orpheus016/integrated-iv-points/software/output/ads1256/volt_log_20260526_152836/volt_log_20260526_152836_transient.png

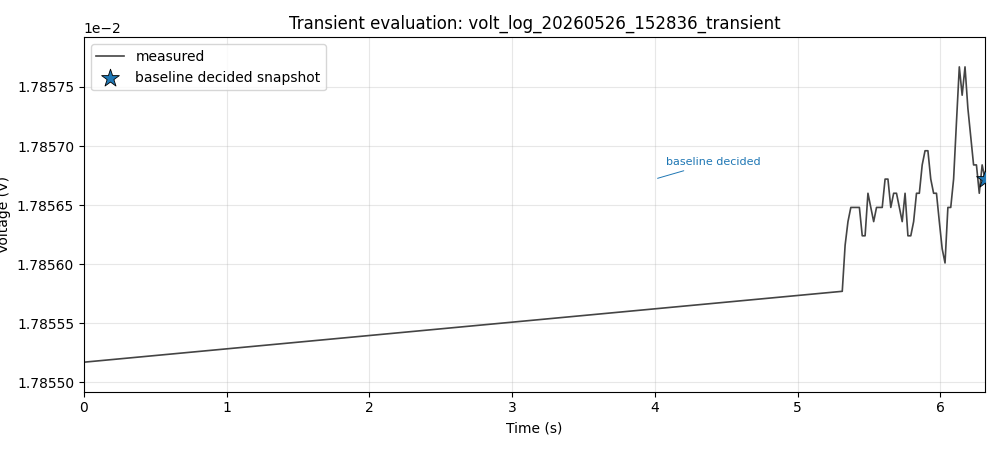
software/output/ads1256/volt_log_20260526_152836/volt_log_20260526_152836_transient.png
