orpheus016/integrated-iv-points/software/output/ads1256/volt_log_20260526_201416/volt_log_20260526_201416_transient.png

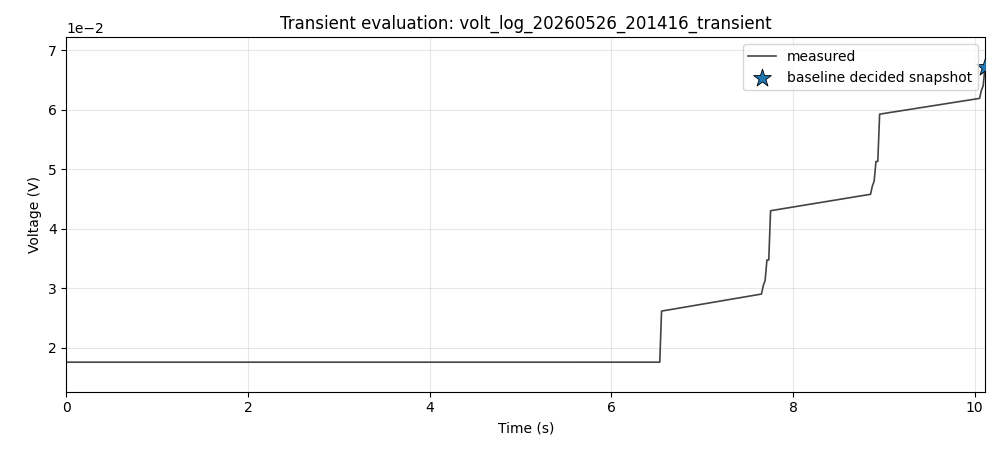
software/output/ads1256/volt_log_20260526_201416/volt_log_20260526_201416_transient.png
