orpheus016/integrated-iv-points/software/output/ads1256/volt_log_20260529_153043/volt_log_20260529_153043_transient.png

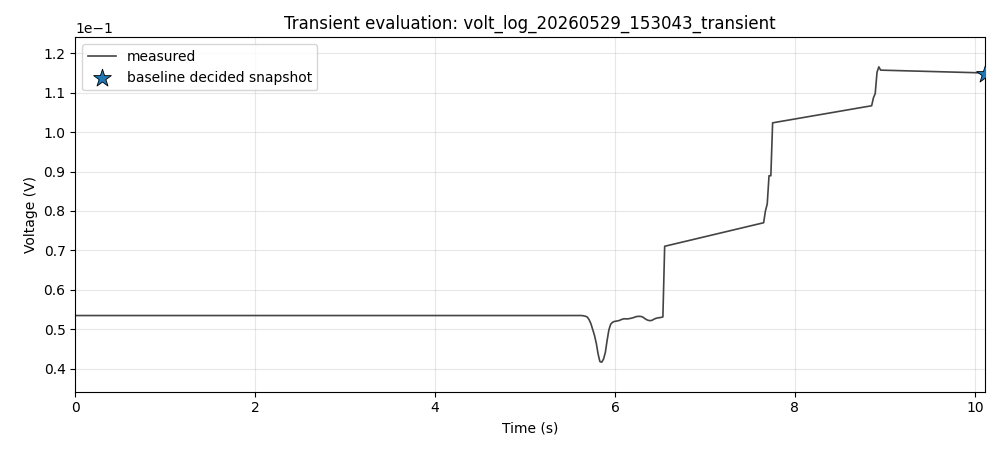
software/output/ads1256/volt_log_20260529_153043/volt_log_20260529_153043_transient.png
