orpheus016/integrated-iv-points/software/output/ads1256/volt_log_20260529_162711/volt_log_20260529_162711_transient.png

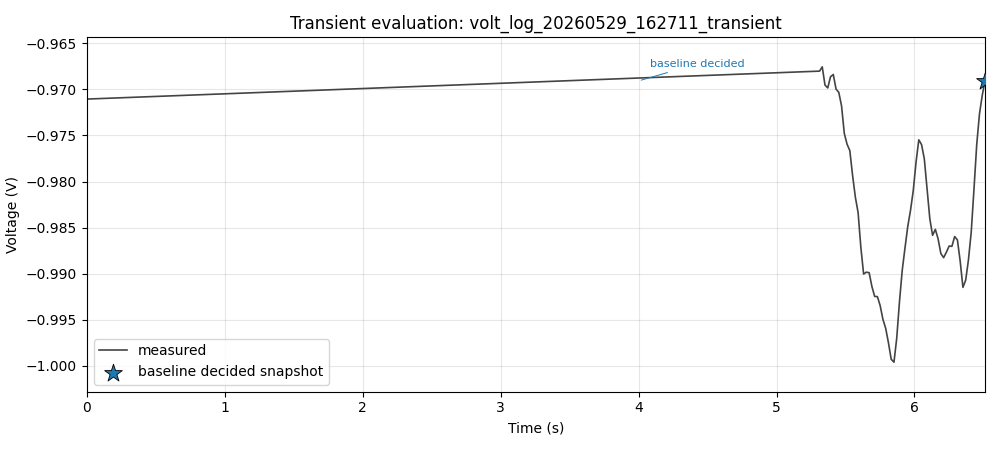
software/output/ads1256/volt_log_20260529_162711/volt_log_20260529_162711_transient.png
