orpheus016/integrated-iv-points/software/output/ads1256/volt_log_20260529_163026/volt_log_20260529_163026_transient.png

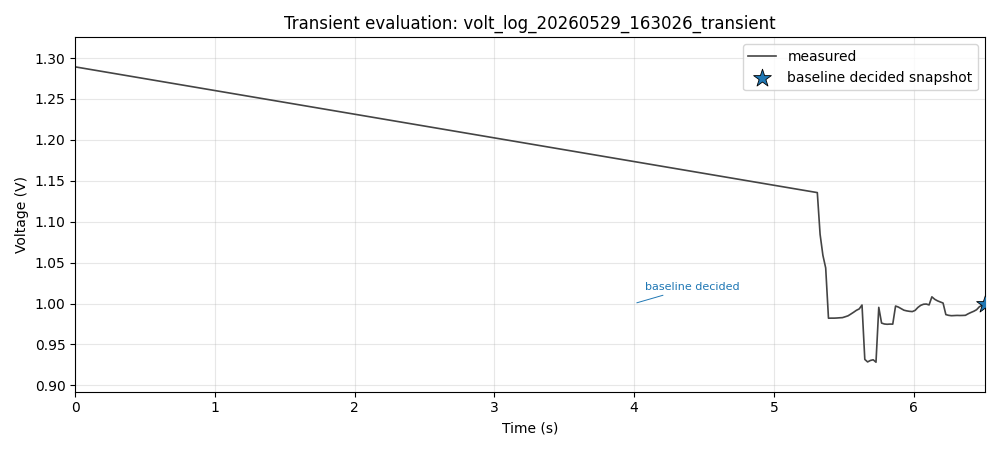
software/output/ads1256/volt_log_20260529_163026/volt_log_20260529_163026_transient.png
