orpheus016/integrated-iv-points/software/output/ads1256/volt_log_20260529_163121/volt_log_20260529_163121_transient.png

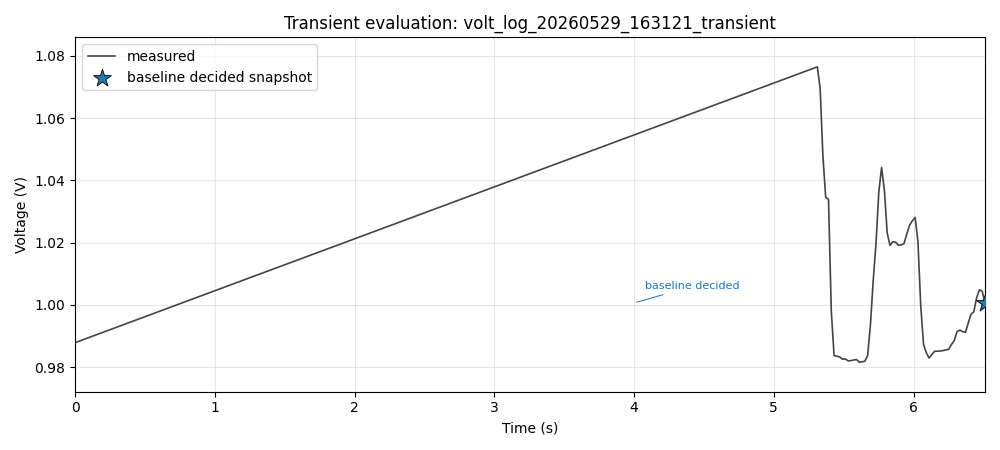
software/output/ads1256/volt_log_20260529_163121/volt_log_20260529_163121_transient.png
