orpheus016/integrated-iv-points/software/output/ads1256/volt_log_20260529_163239/volt_log_20260529_163239_transient.png

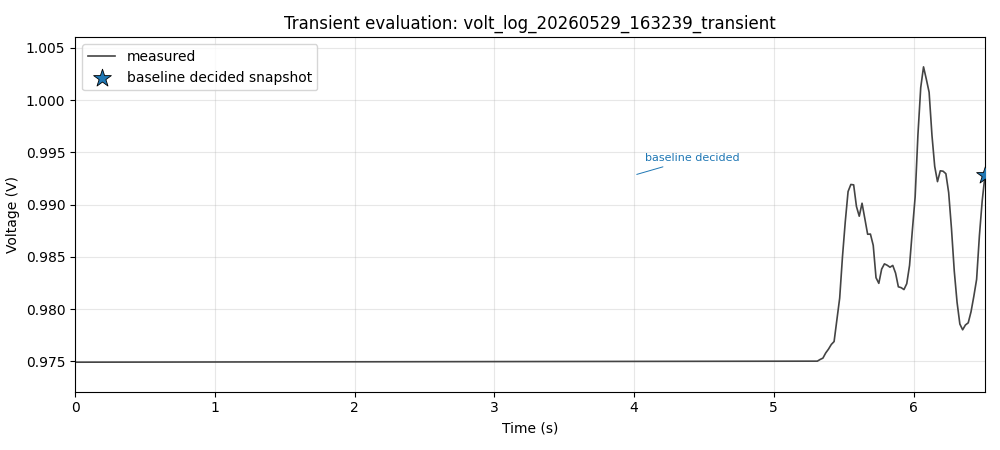
software/output/ads1256/volt_log_20260529_163239/volt_log_20260529_163239_transient.png
