orpheus016/integrated-iv-points/software/output/ads1256/volt_log_20260529_163329/volt_log_20260529_163329_transient.png

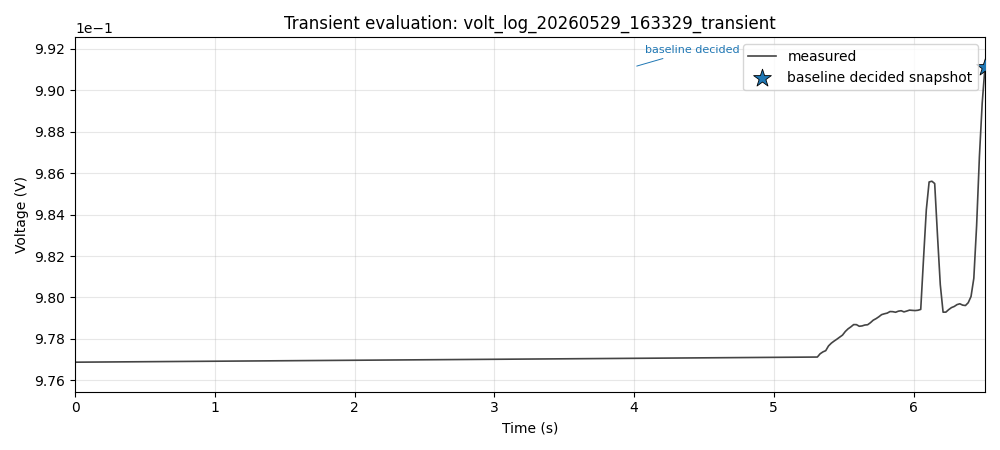
software/output/ads1256/volt_log_20260529_163329/volt_log_20260529_163329_transient.png
