orpheus016/integrated-iv-points/software/plots/output/current_source_consistency/current_source_consistency_plot_integrated.png

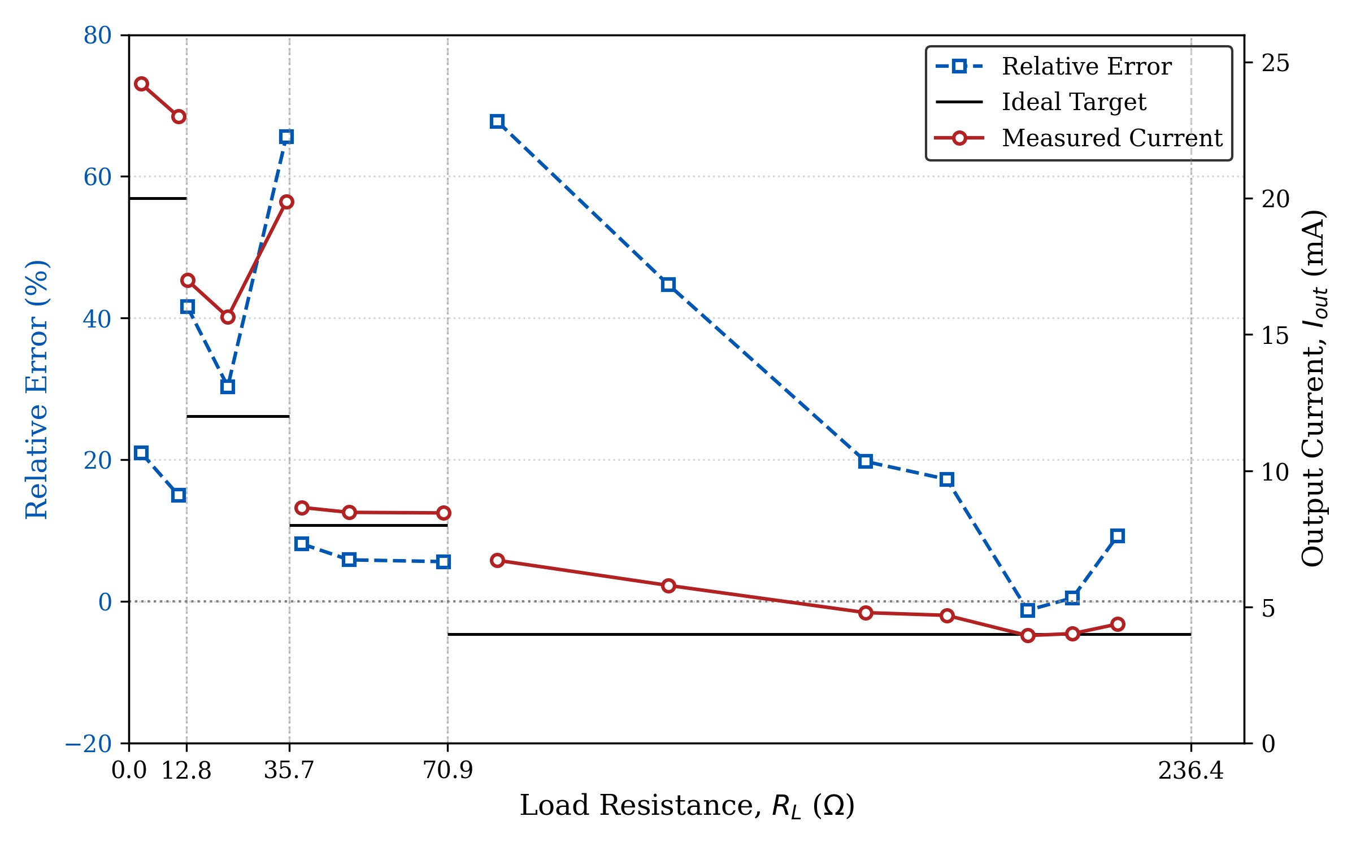
software/plots/output/current_source_consistency/current_source_consistency_plot_integrated.png
