orpheus016/integrated-iv-points/software/plots/output/current_source_consistency/research_grade_stability_plot.png

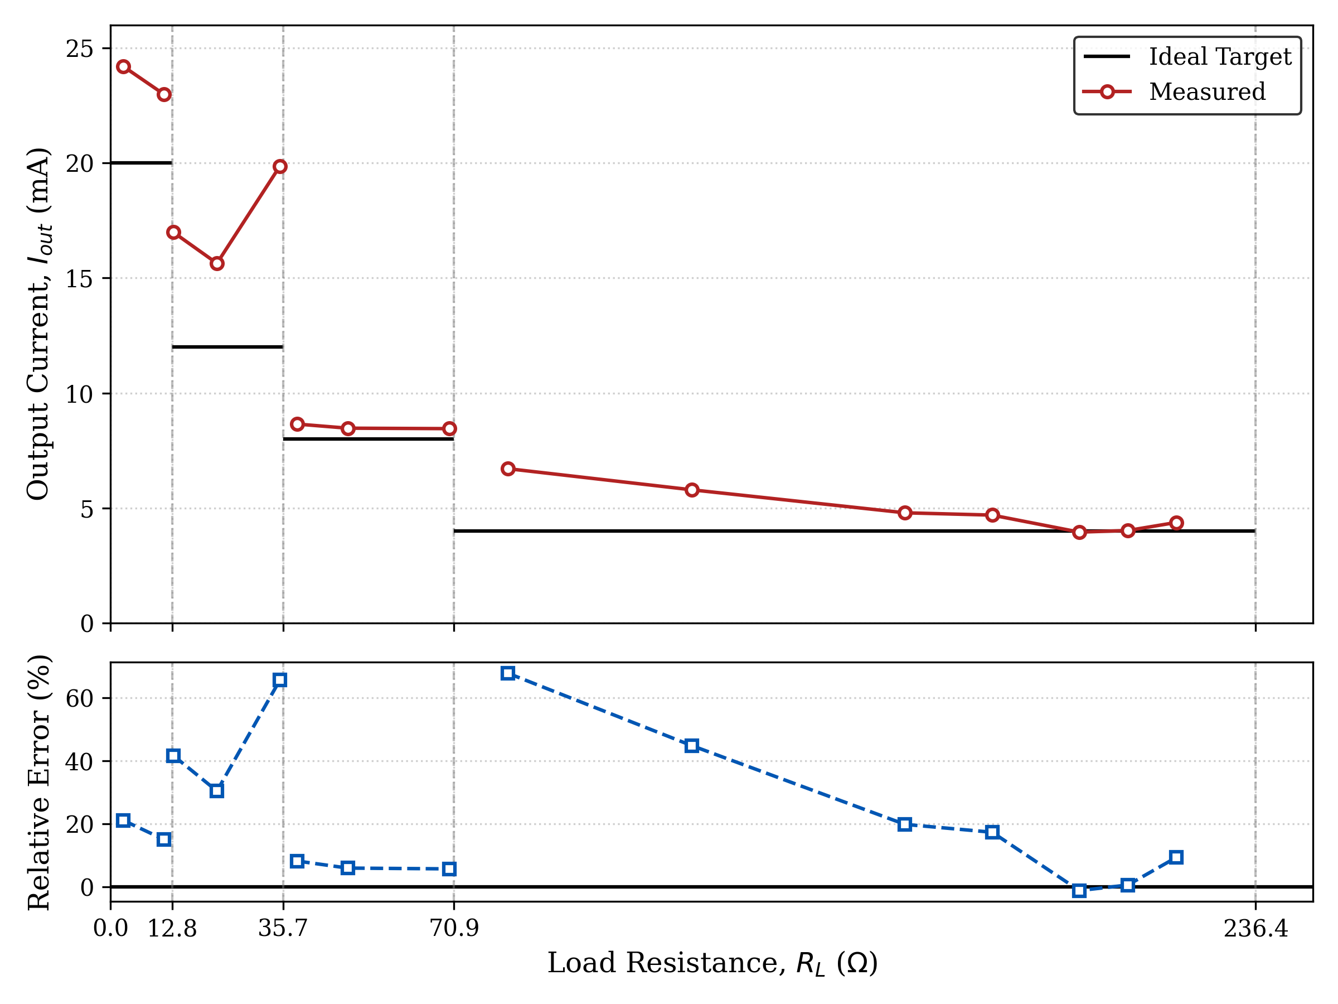
software/plots/output/current_source_consistency/research_grade_stability_plot.png
