orpheus016/integrated-iv-points/software/plots/output/ia_dc/ia_dc_transfer_analysis.png

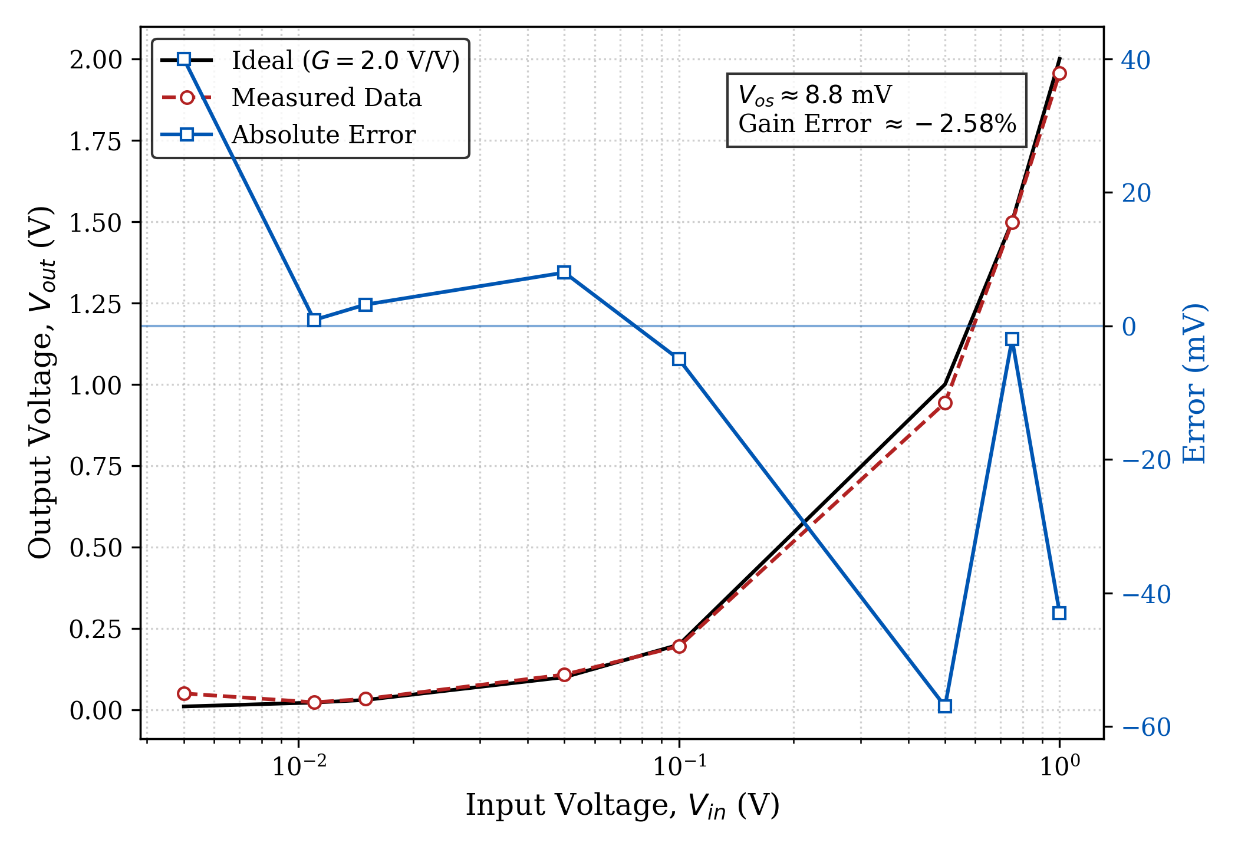
software/plots/output/ia_dc/ia_dc_transfer_analysis.png
