orpheus016/integrated-iv-points/software/plots/output/signal_quality/signal_quality_combined.png

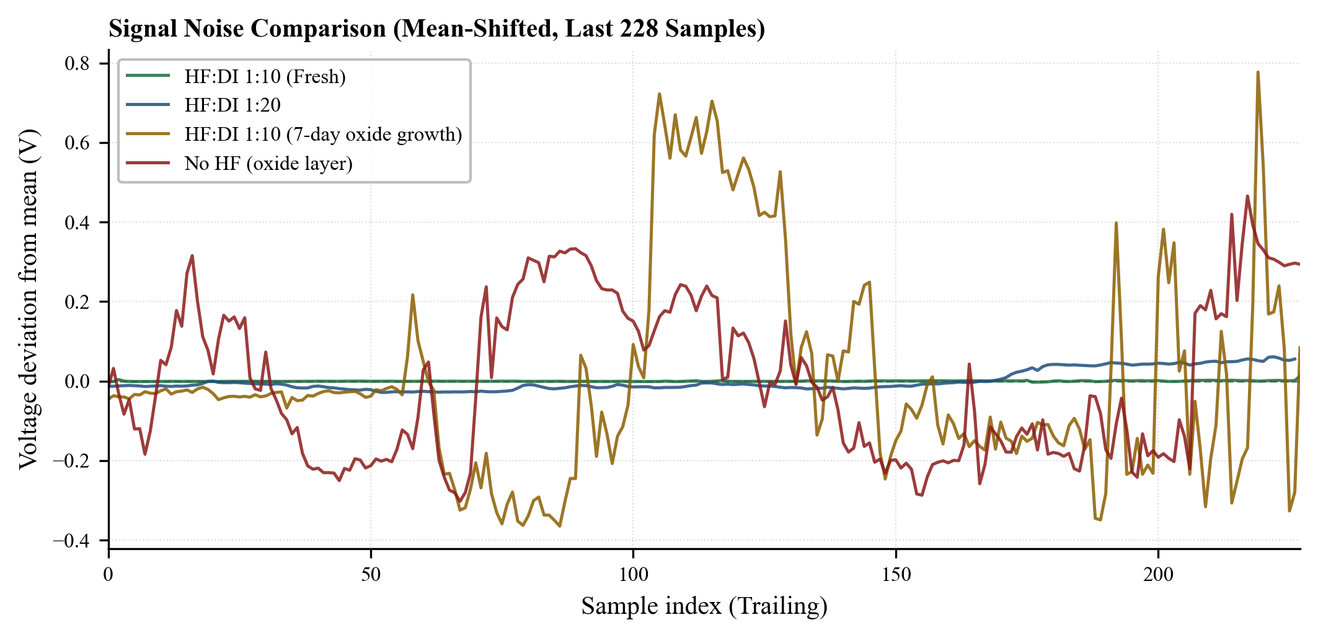
software/plots/output/signal_quality/signal_quality_combined.png
