orpheus016/integrated-iv-points/software/plots/output/temporal_robustness/20260607_012642/boxplot.png

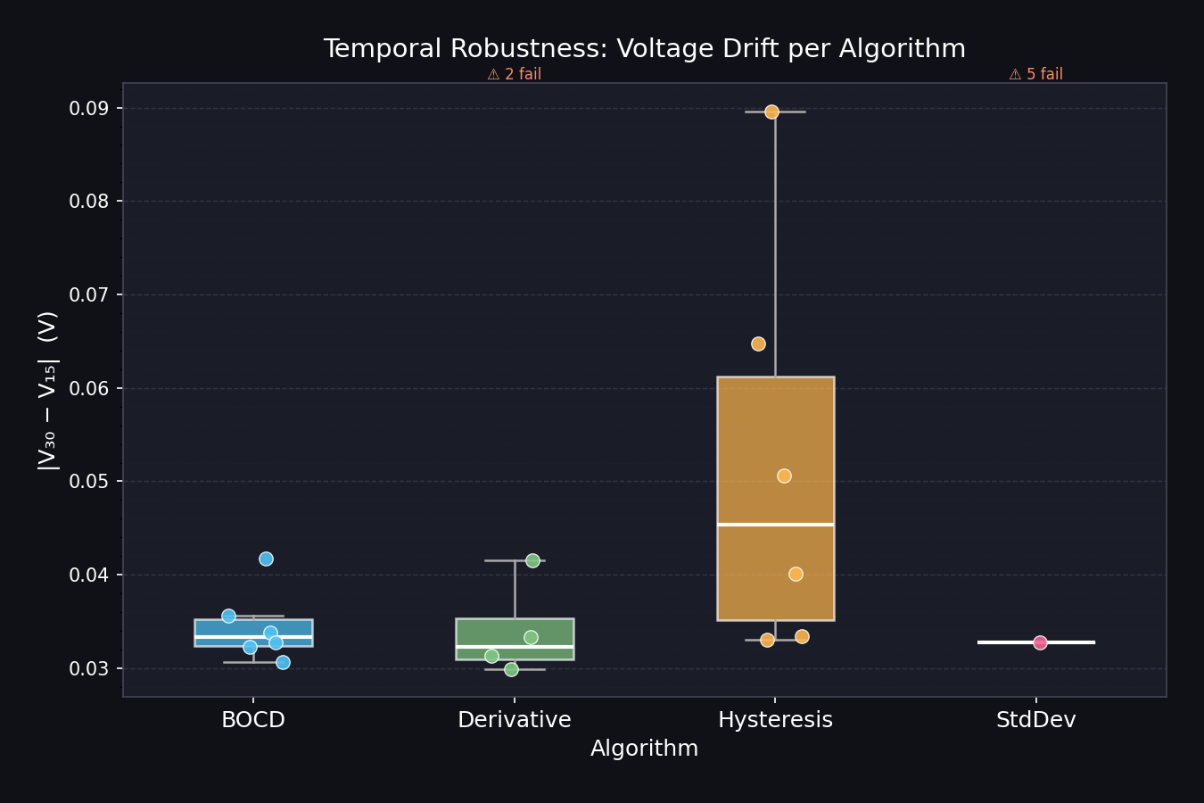
software/plots/output/temporal_robustness/20260607_012642/boxplot.png
