orpheus016/integrated-iv-points/software/plots/output/temporal_robustness/20260607_023558/boxplot.png

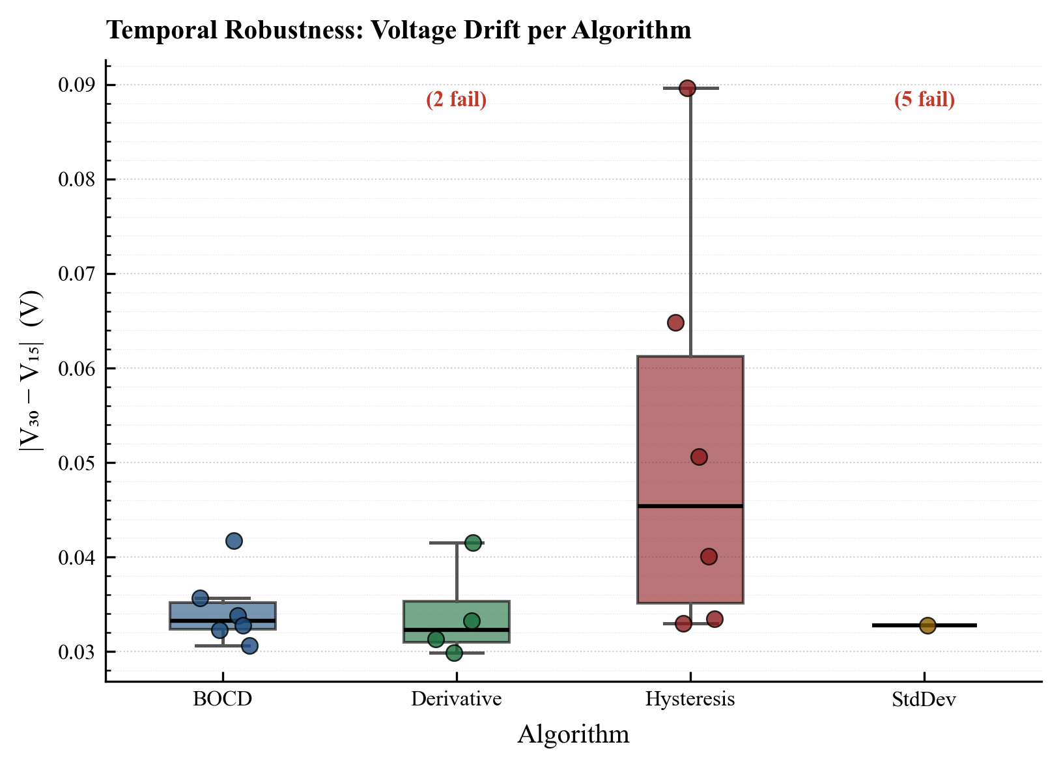
software/plots/output/temporal_robustness/20260607_023558/boxplot.png
