orpheus016/integrated-iv-points/software/plots/output/voltmeter_stability/adc_metrology_analysis.png

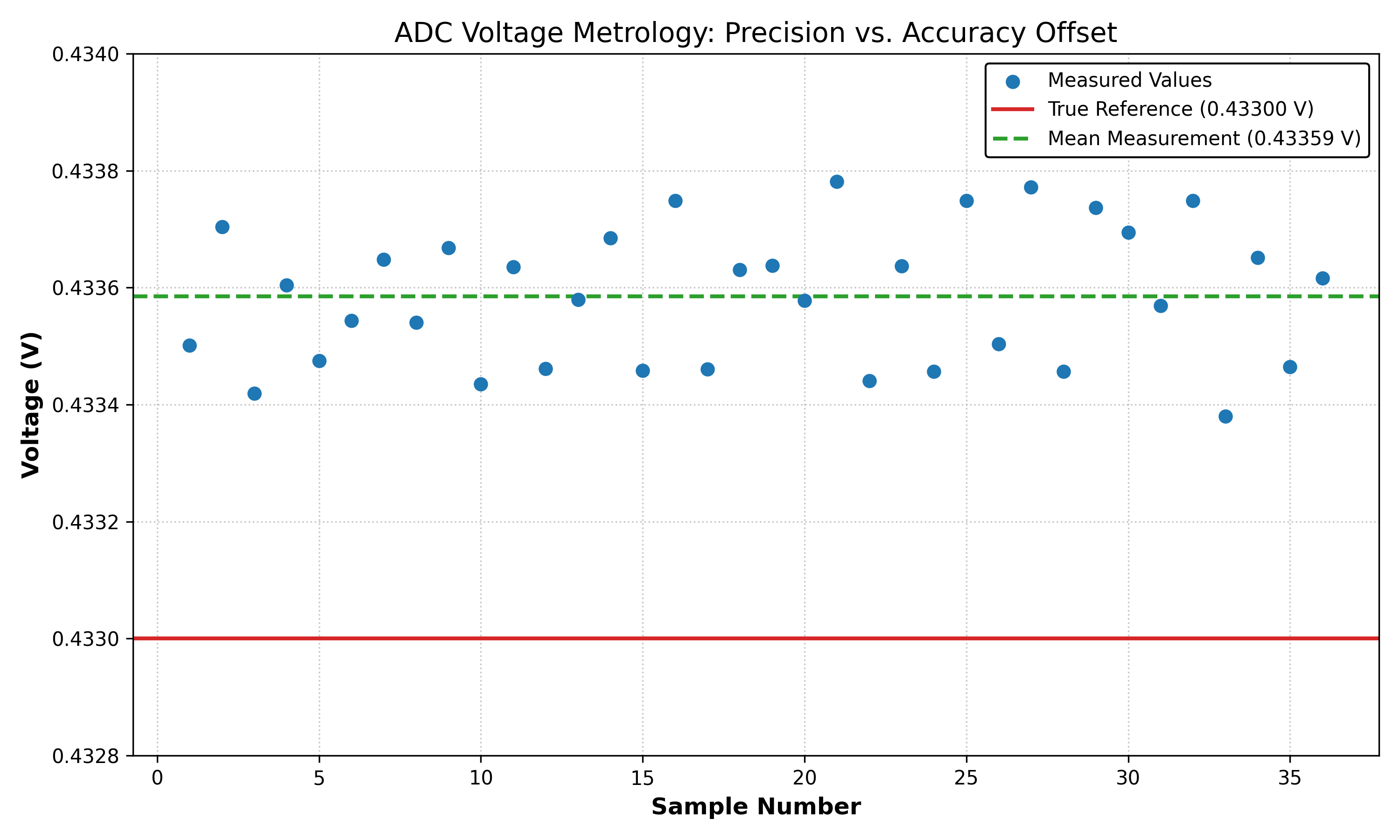
software/plots/output/voltmeter_stability/adc_metrology_analysis.png
