orpheus016/integrated-iv-points/software/output/evaluate/CSwithIA5/baseline/CSwithIA5.png

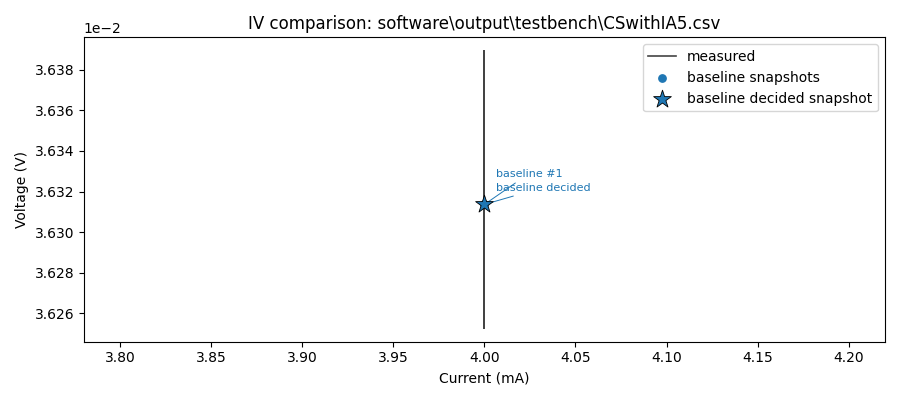
software/output/evaluate/CSwithIA5/baseline/CSwithIA5.png
