orpheus016/integrated-iv-points/software/output/evaluate/settling/settling-testbench.png

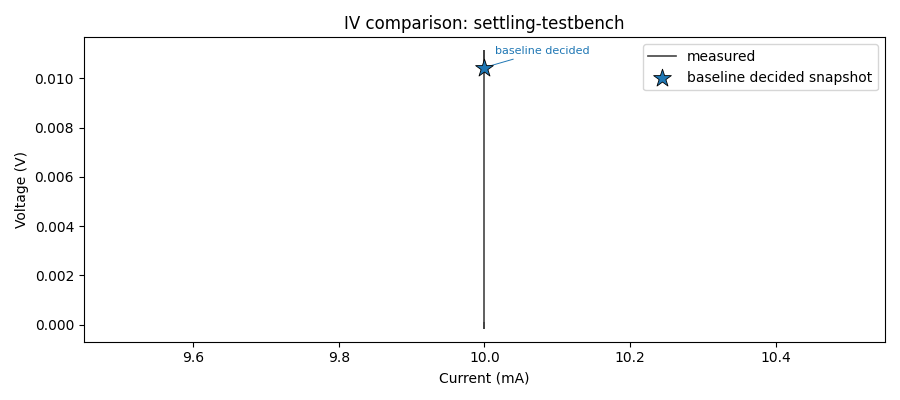
software/output/evaluate/settling/settling-testbench.png
