orpheus016/integrated-iv-points/software/output/evaluate/settling/transient-demo/settling-testbench.png

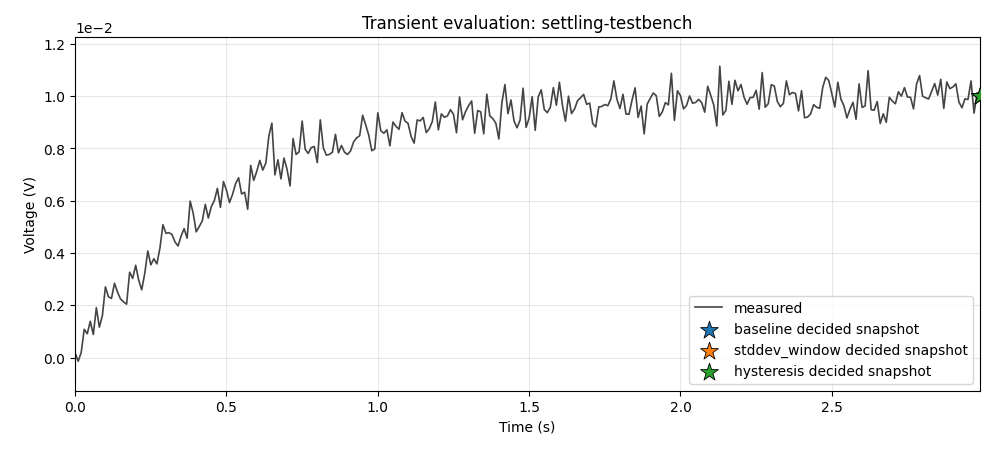
software/output/evaluate/settling/transient-demo/settling-testbench.png
