orpheus016/integrated-iv-points/software/output/evaluate/stable20mA/baseline/stable20mA.png

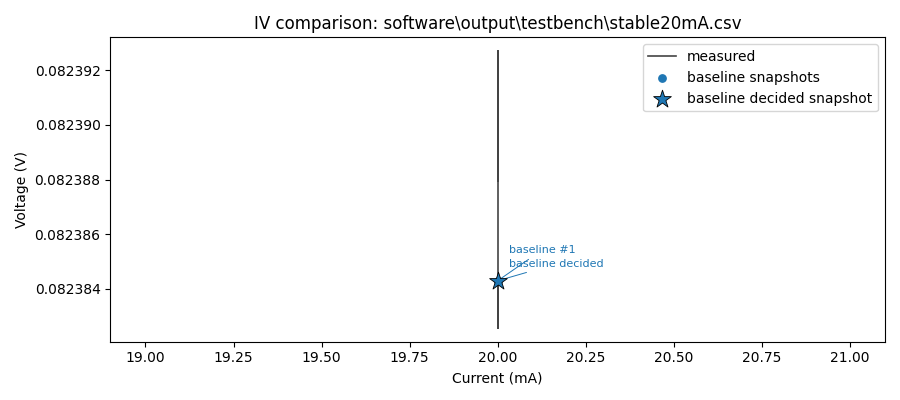
software/output/evaluate/stable20mA/baseline/stable20mA.png
