orpheus016/integrated-iv-points/software/output/evaluate/stable20mA/transient-demo/stable20mA.png

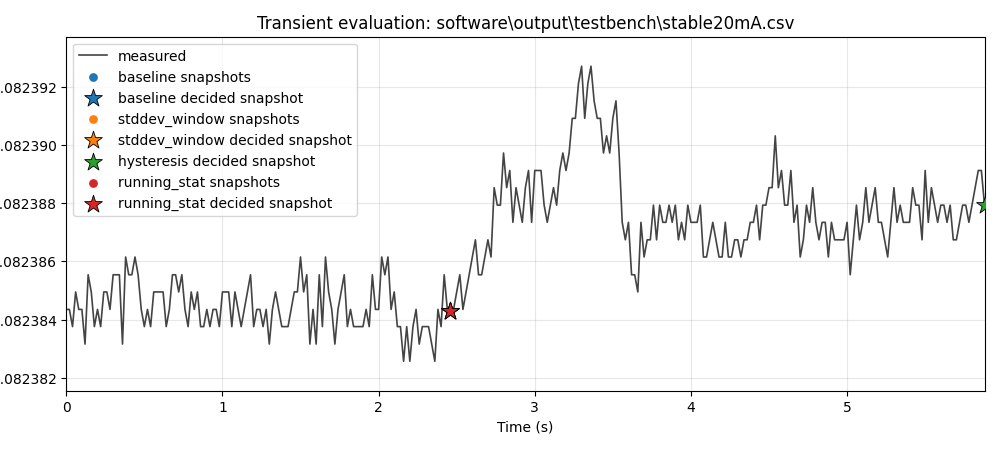
software/output/evaluate/stable20mA/transient-demo/stable20mA.png
