orpheus016/integrated-iv-points/software/output/evaluate/stable20mALONG/transient-demo/stable20mALONG.png

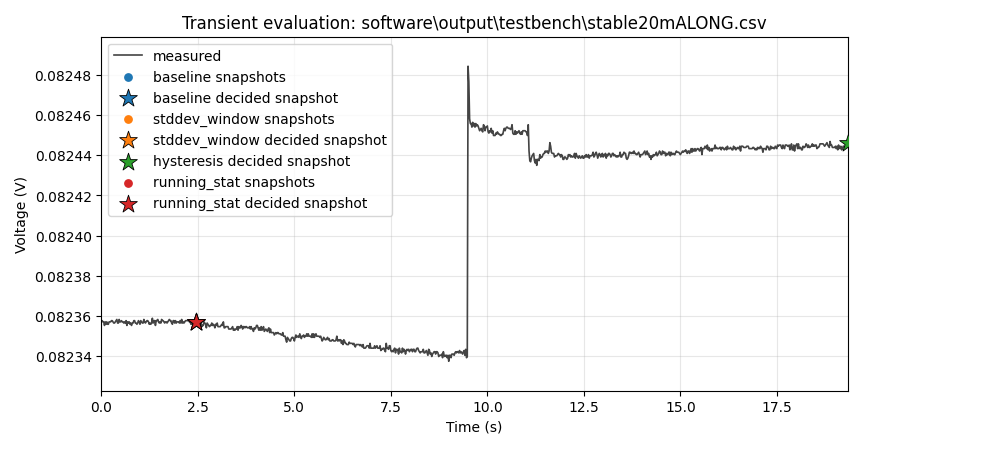
software/output/evaluate/stable20mALONG/transient-demo/stable20mALONG.png
