orpheus016/integrated-iv-points/software/output/evaluate/waferIA6/transient-demo/waferIA6.png

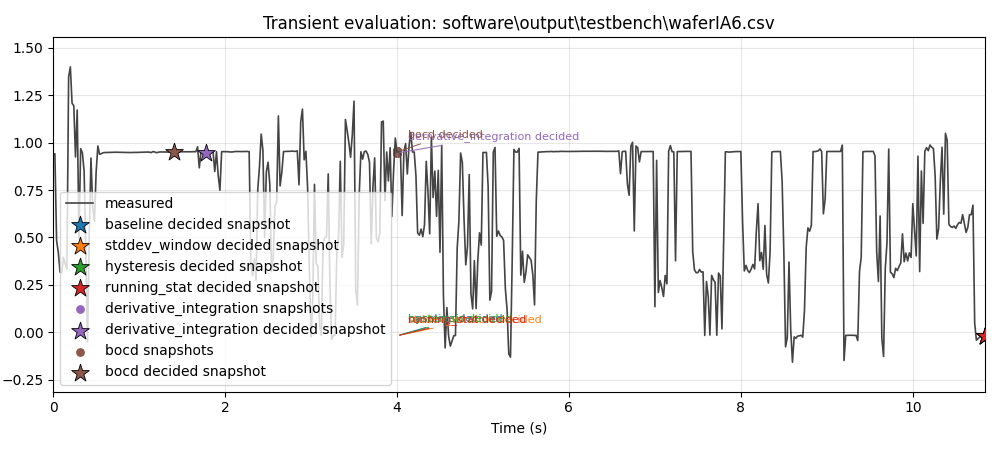
software/output/evaluate/waferIA6/transient-demo/waferIA6.png
