orpheus016/integrated-iv-points/software/output/evaluate/worst_case/transient-demo/worst_case-testbench.png

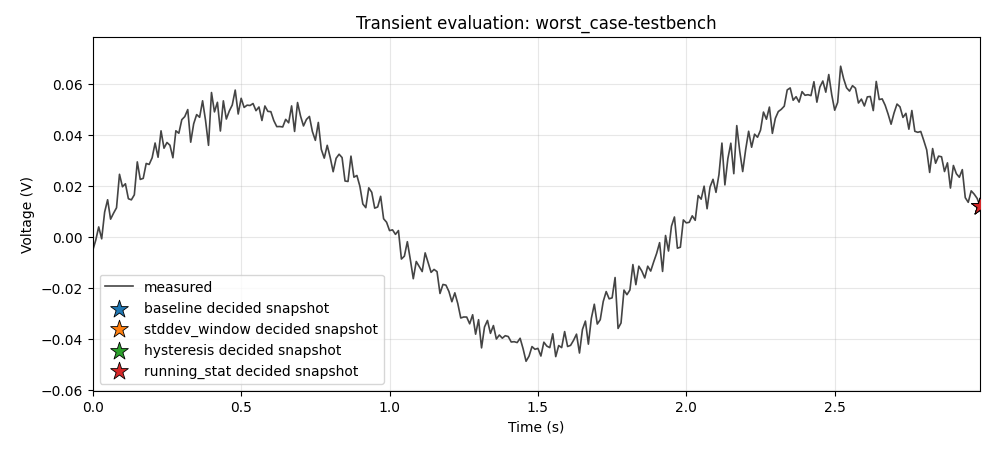
software/output/evaluate/worst_case/transient-demo/worst_case-testbench.png
