orpheus016/integrated-iv-points/software/plots/output/algorithm_benchmark/algorithm_tradeoff.png

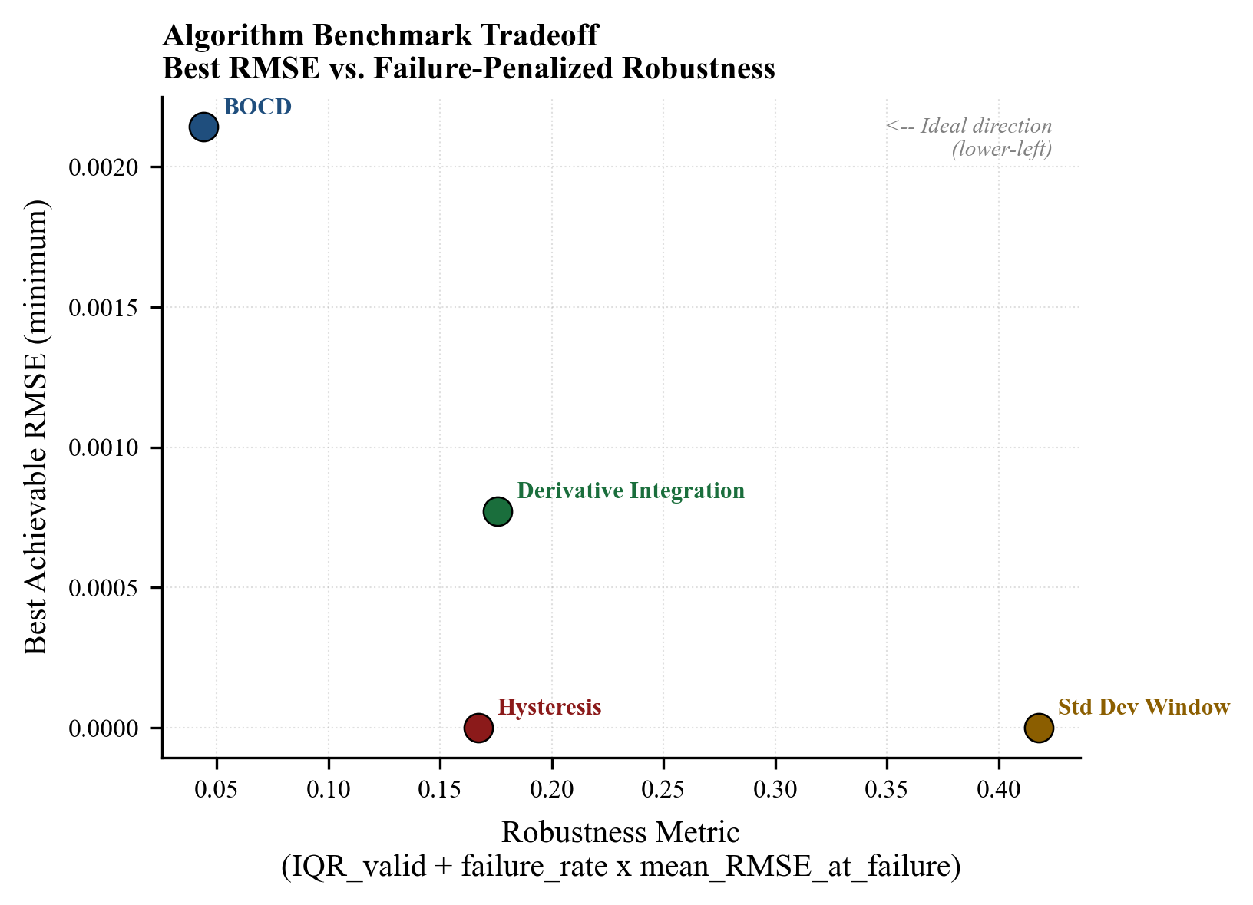
software/plots/output/algorithm_benchmark/algorithm_tradeoff.png
